tanmoydutta/ScrollMouse/images/BearingHolder.png

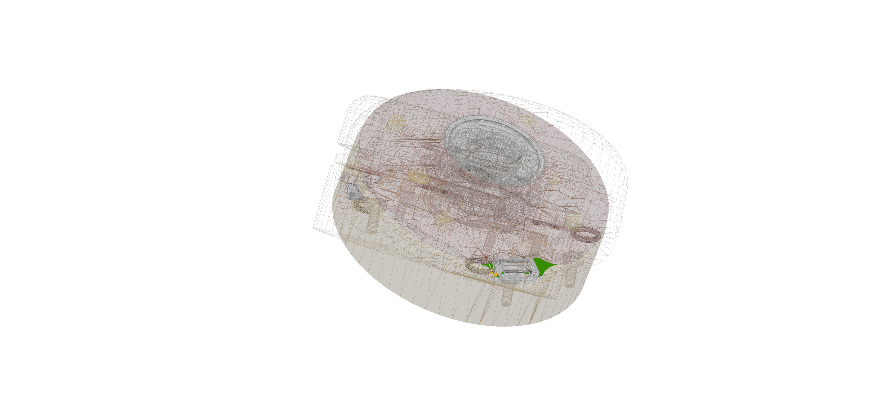
images/BearingHolder.png
