tanmoydutta/ScrollMouse/images/PCB.png

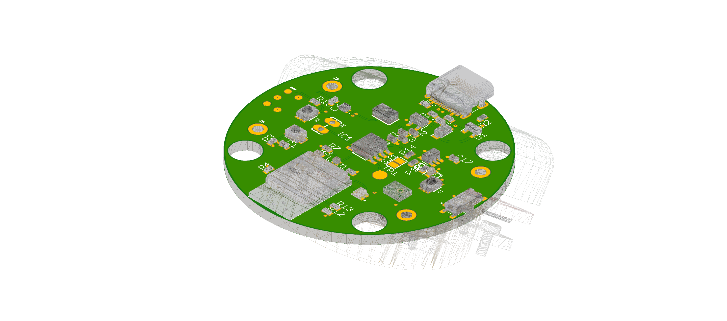
images/PCB.png
